beantowel/SimTouch/code/Slave/SimCap.ioc

Mcu.UserName=STM32F103C8Tx
PA1.Signal=GPIO_Output
PA11.Signal=USB_DM
PA12.Signal=USB_DP
PA13.Signal=SYS_JTMS-SWDIO
PA14.Signal=SYS_JTCK-SWCLK
PA2.Signal=GPIO_Output
PA3.Signal=GPIO_Output
PA4.Signal=GPIO_Output
PC13-TAMPER-RTC.Signal=GPIO_Output
PC14-OSC32_IN.Signal=RCC_OSC32_IN
PC15-OSC32_OUT.Signal=RCC_OSC32_OUT
PD0-OSC_IN.Signal=RCC_OSC_IN
PD1-OSC_OUT.Signal=RCC_OSC_OUT
